revk/ESP32-Faikin/PCB/Faikin2/Faikin/Faikin.kicad_sch

## KiCad design PCB/Faikin2/Faikin/Faikin.kicad_sch (2023-07-15)

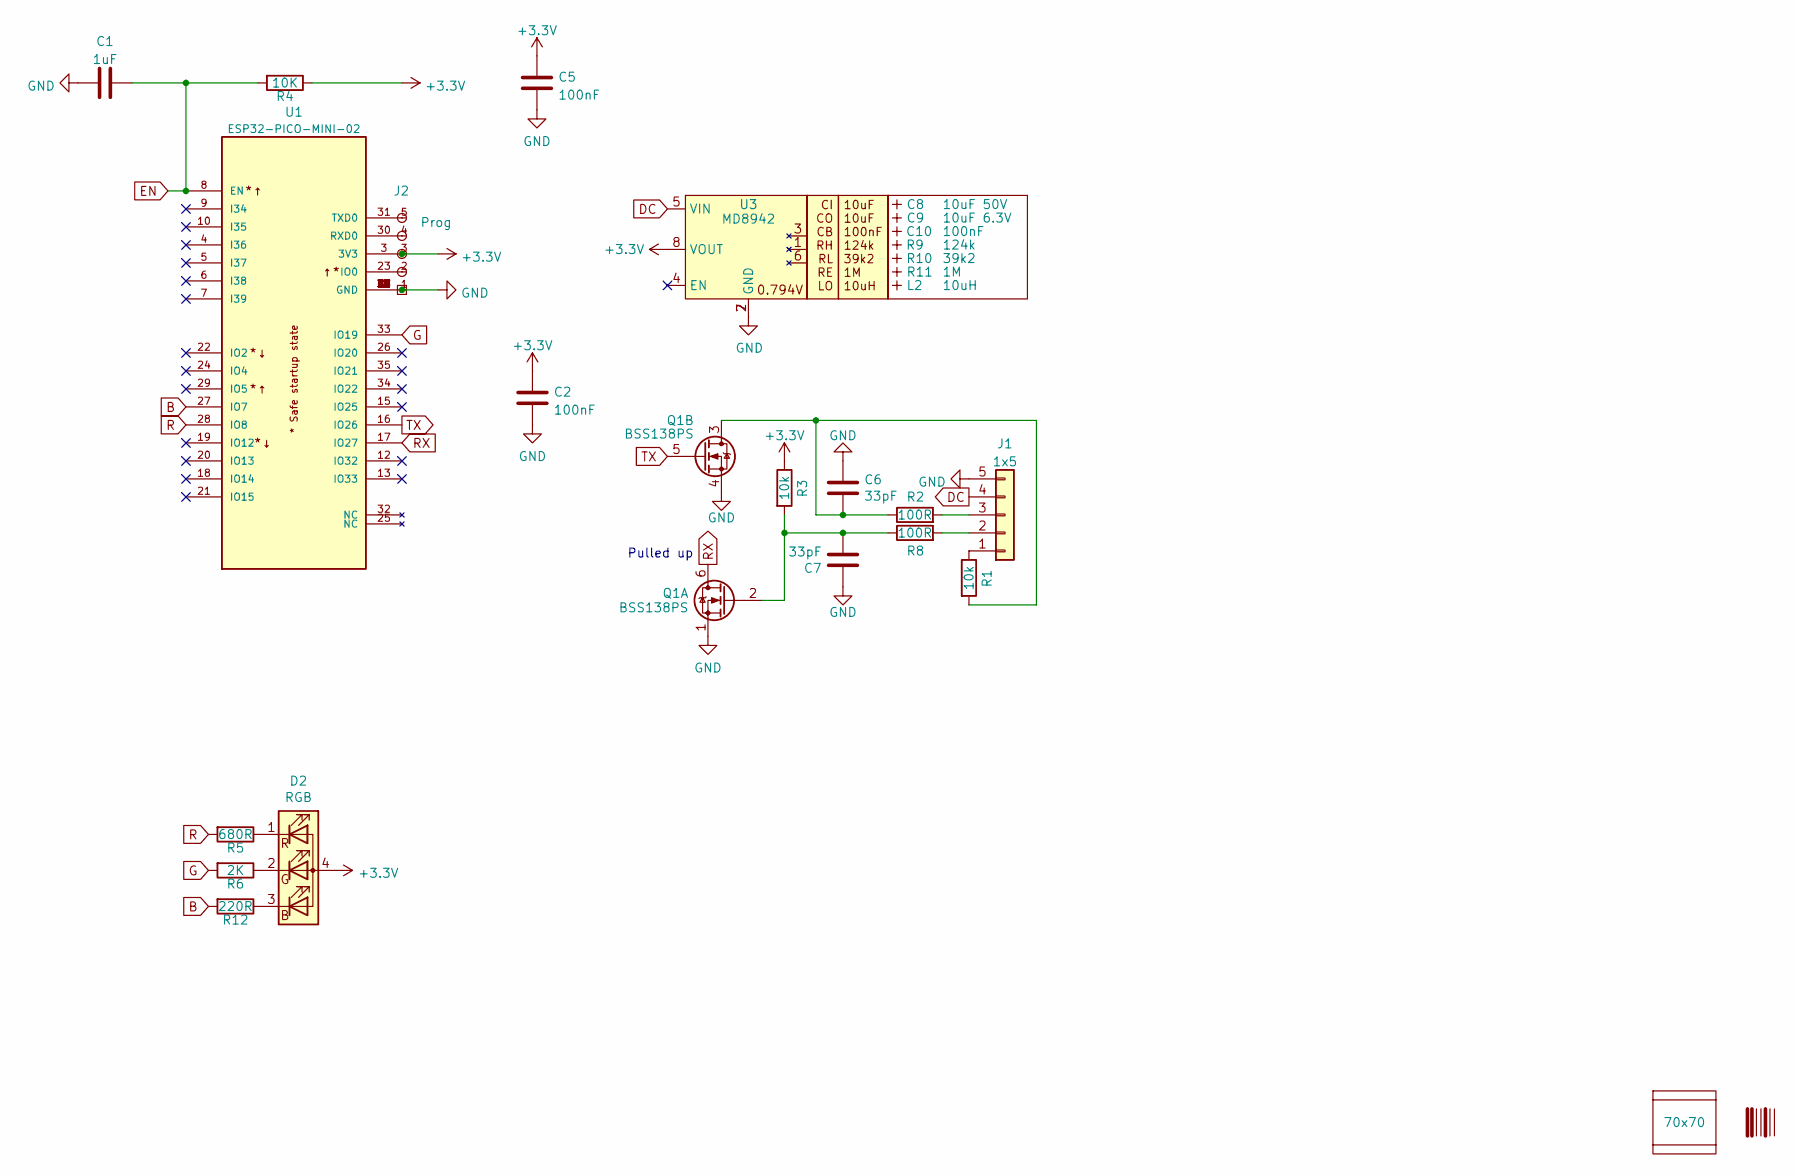
[picture p33: schematic Faikin.kicad_sch]

Parts:
C1: 1uF; C_0402
C2, C5: 100nF; C_0402
C6, C7: 33pF; C_0402
C8: 10uF 50V; C_0603_; LCSC Part # C1591
C9: 10uF 6.3V; C_0603_; LCSC Part # C1691
C10: 100nF; C_0603_
D2: RGB; LED-RGB-1.6x1.6; Part No APTF1616LSEEZGKQBKC; LCSC Part # C264508
J1: 1x5; JST_EH_S5B-EH_1x05_P2.50mm_Horizontal; LCSC Part # C225427
J2: Prog; Shelly
L2: 10uH; L_4x4_
PCB1: 70x70; PCB7070
Q1: BSS138PS; SOT-363_SC-70-6; LCSC Part # C193381
R1, R3: 10k; R_0402
R2, R8: 100R; R_0402
R4: 10K; R_0402
R5: 680R; R_0402
R6: 2K; R_0402
R9: 124k; R_0402_
R10: 39k2; R_0402_
R11: 1M; R_0402_
R12: 220R; R_0402
U1: ESP32-PICO-MINI-02; PARTREV v1.0; LCSC Part # C2980306
U2: Barcode; EAN-5060634238151
U3: MD8942; SOT-23-6-MD8942; LCSC Part # C2684786
V1, V2: VCUT70

Connections:
+3.3V: C2.1, C5.1, D2.4 (A), J2.3 (3V3), R3.1, R4.1, U1.3 (3V3), U3.8 (VOUT)
B: R12.2, U1.27 (IO7)
DC: J1.4, U3.5 (VIN)
EN: C1.2, R4.2, U1.8 (EN)
G: R6.2, U1.33 (IO19)
GND: C1.1, C2.2, C5.2, C6.1, C7.1, J1.5, J2.1 (GND), Q1.1 (SN), Q1.4 (SP), U1.1 (GND), U1.2 (GND), U1.11 (GND), U1.14 (GND), U1.36 (GND), U1.37 (GND), U1.38 (GND), U1.39 (GND), U1.40 (GND), U1.41 (GND), U1.42 (GND), U1.43 (GND), U1.44 (GND), U1.45 (GND), U1.46 (GND), U1.47 (GND), U1.48 (GND), U1.49 (GND), U1.50 (GND), U1.51 (GND), U1.52 (GND), U1.53 (GND), U3.2 (GND), U3.7 (GND)
unnamed: C6.2, Q1.3 (DP), R1.2, R2.1
unnamed: C7.2, Q1.2 (GN), R3.2, R8.1
unnamed: D2.1 (RK), R5.1
unnamed: D2.2 (GK), R6.1
unnamed: D2.3 (BK), R12.1
unnamed: J1.1, R1.1
unnamed: J1.2, R8.2
unnamed: J1.3, R2.2
unnamed: J2.2 (0), U1.23 (IO0)
unnamed: J2.4 (Rx), U1.30 (RXD0)
unnamed: J2.5 (Tx), U1.31 (TXD0)
R: R5.2, U1.28 (IO8)
RX: Q1.6 (DN), U1.17 (IO27)
TX: Q1.5 (GP), U1.16 (IO26)

Notes on the sheet:
Pulled up
